jhawthorn/modelh/site/16_8_4.jpg

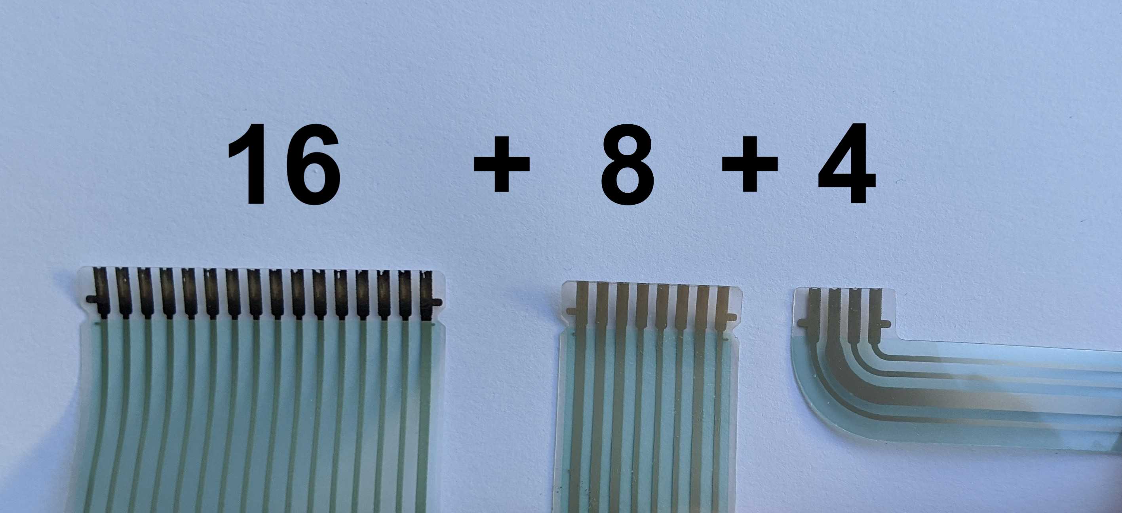
site/16_8_4.jpg
