jhawthorn/modelh/site/16_12.jpg

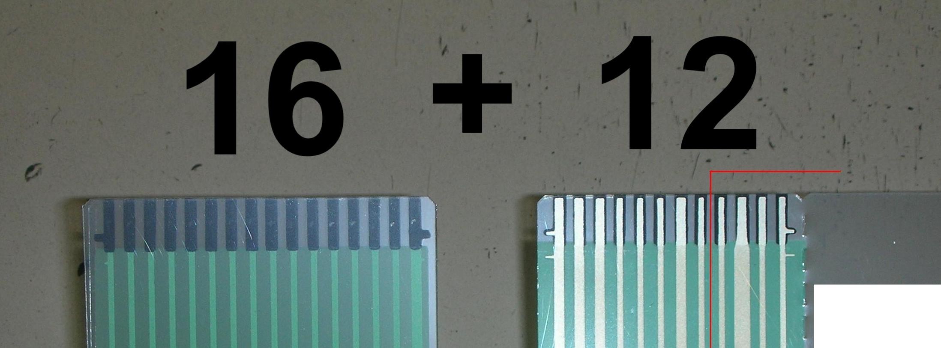
site/16_12.jpg
